Mac-Adam/weather_station_2/3dModels/hub/cover.3mf

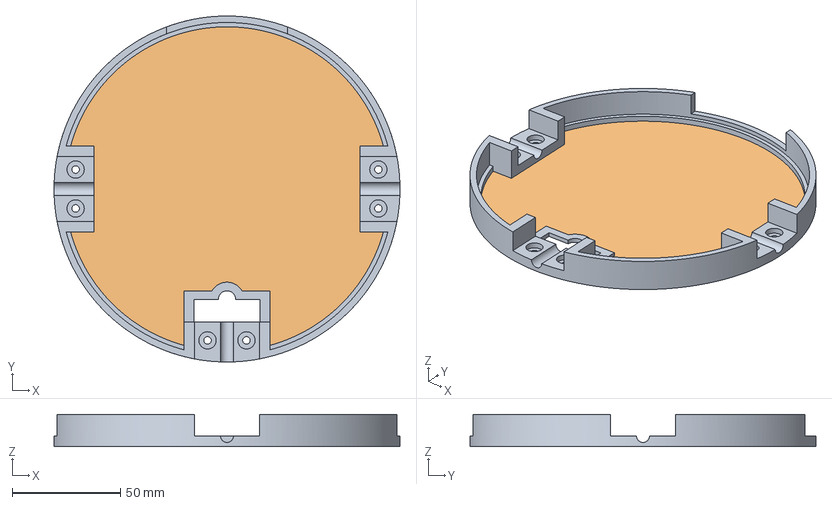
[picture p15: CAD file, 2026-03-01]
3dModels/hub/cover.3mf
160.0 x 160.0 x 15.0 mm
