Mac-Adam/weather_station_2/3dModels/rain/pools.3mf

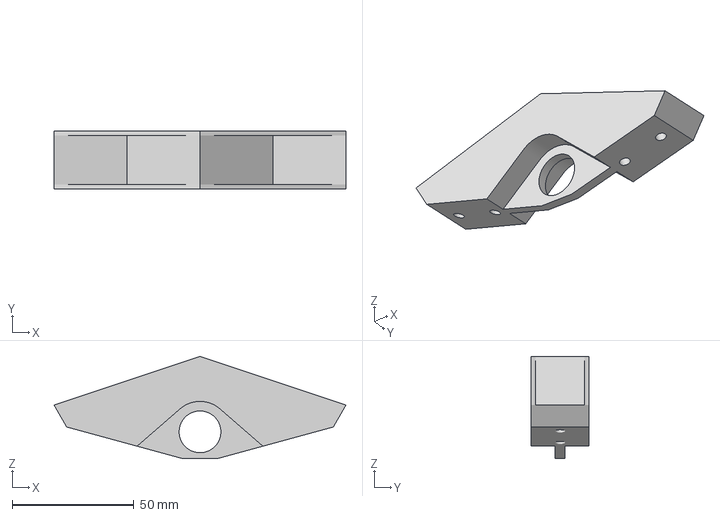
[picture p16: CAD file, 2026-03-01]
3dModels/rain/pools.3mf
120.0 x 24.0 x 42.0 mm
