Mac-Adam/weather_station_2/3dModels/wind/cover.3mf

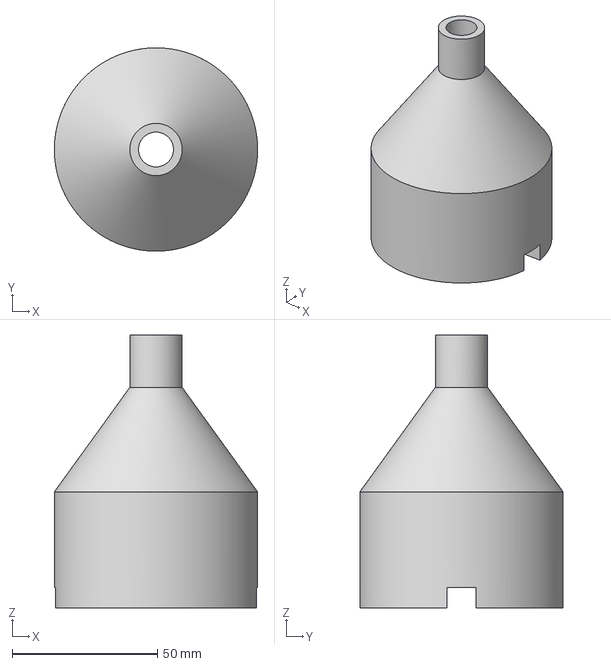
[picture p17: CAD file, 2026-03-01]
3dModels/wind/cover.3mf
70.0 x 70.0 x 94.0 mm
