Mac-Adam/weather_station_2/3dModels/rain/mout.3mf

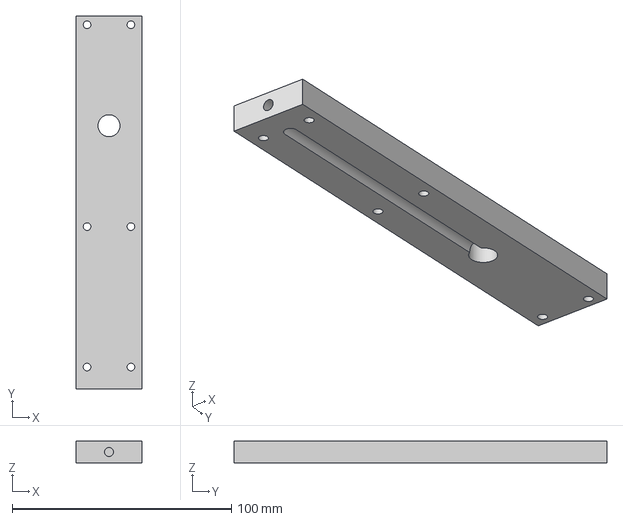
[picture p18: CAD file, 2026-03-01]
3dModels/rain/mout.3mf
30.0 x 170.0 x 10.0 mm
