Mac-Adam/weather_station_2/3dModels/wind/shaft_speed.3mf

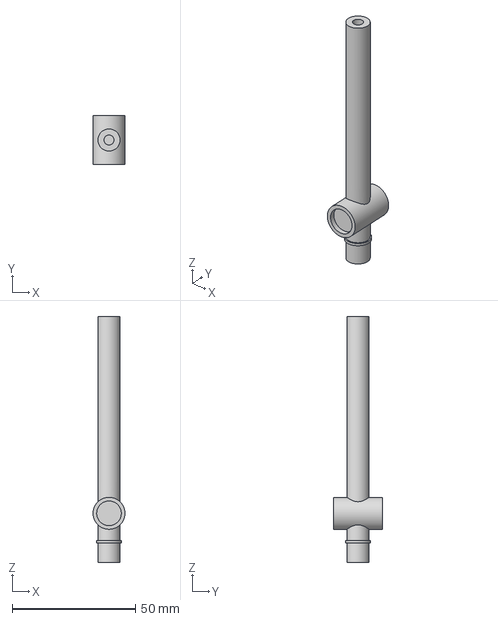
[picture p19: CAD file, 2026-03-01]
3dModels/wind/shaft_speed.3mf
13.0 x 20.0 x 100.0 mm
