Mac-Adam/weather_station_2/3dModels/hub/mount.3mf

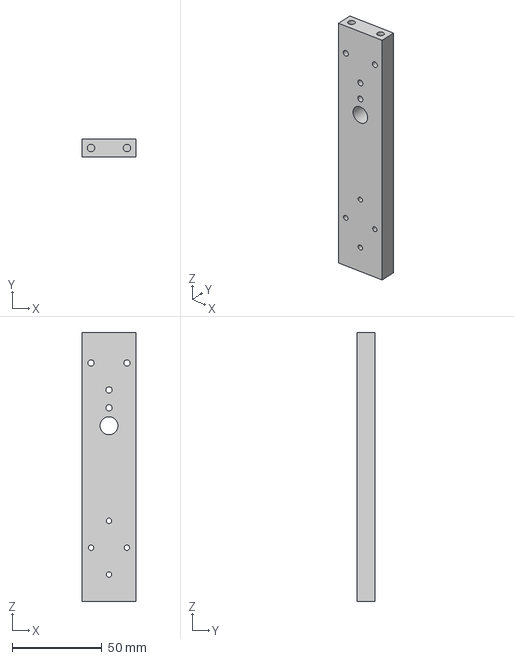
[picture p20: CAD file, 2026-03-01]
3dModels/hub/mount.3mf
30.0 x 10.0 x 150.0 mm
