Mac-Adam/weather_station_2/3dModels/rain/pin_holder.3mf

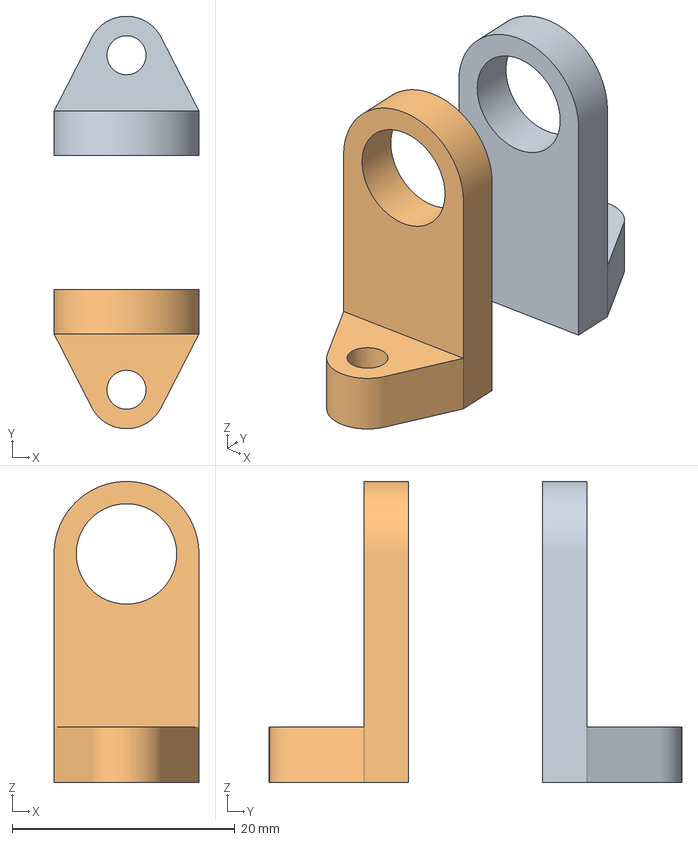
[picture p21: CAD file, 2026-03-01]
3dModels/rain/pin_holder.3mf
13.0 x 37.0 x 27.0 mm
