Mac-Adam/weather_station_2/3dModels/wind/mount.3mf

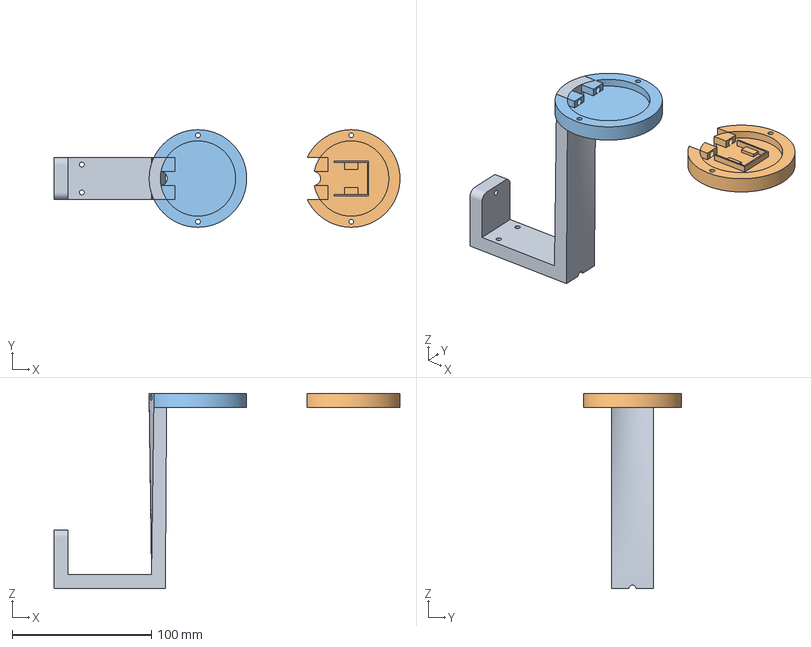
[picture p22: CAD file, 2026-03-01]
3dModels/wind/mount.3mf
248.3 x 70.0 x 140.0 mm
wind_base_mount
wind_direction_mount
wind_speed_mount
