Mac-Adam/weather_station_2/3dModels/hub/cover_minimal.3mf

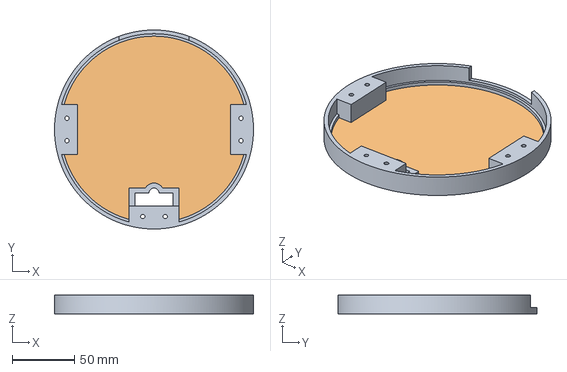
[picture p23: CAD file, 2026-03-01]
3dModels/hub/cover_minimal.3mf
160.0 x 160.0 x 15.0 mm
