Mac-Adam/weather_station_2/3dModels/rain/body.3mf

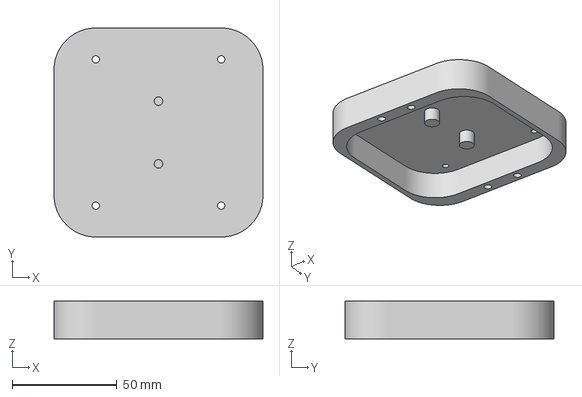
[picture p24: CAD file, 2026-03-01]
3dModels/rain/body.3mf
100.0 x 100.0 x 18.0 mm
