Mac-Adam/weather_station_2/3dModels/wind/top_cover.3mf

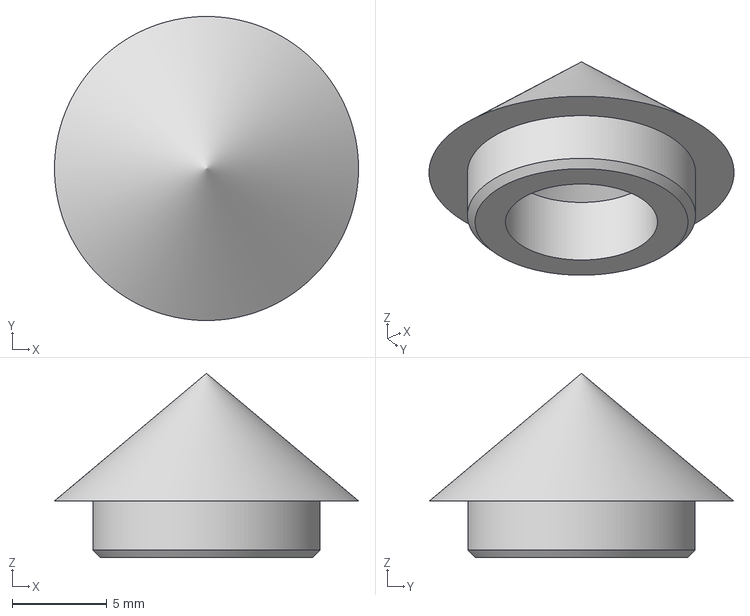
[picture p25: CAD file, 2026-03-01]
3dModels/wind/top_cover.3mf
16.1 x 16.1 x 9.73 mm
