Mac-Adam/weather_station_2/3dModels/rain/maget_holder.3mf

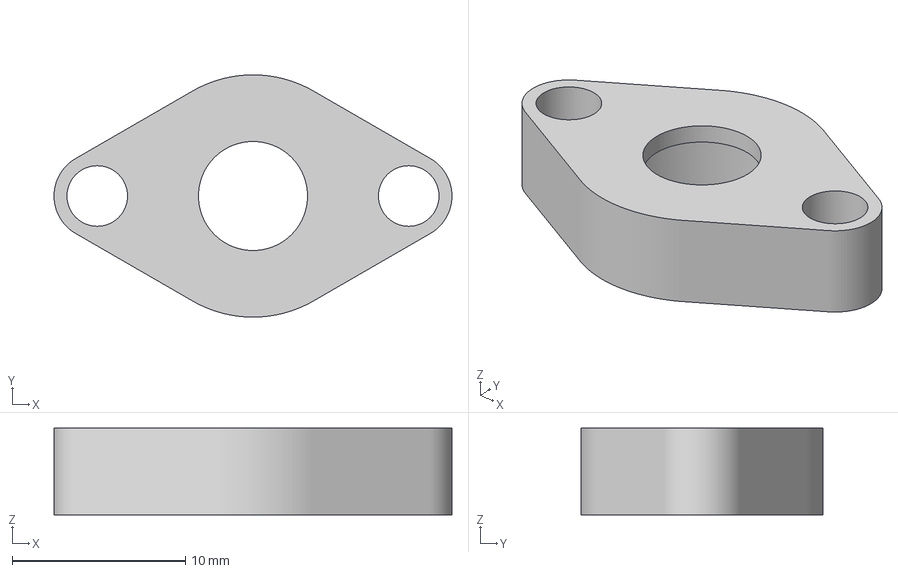
[picture p26: CAD file, 2026-03-01]
3dModels/rain/maget_holder.3mf
23.0 x 14.0 x 5.00 mm
