Mac-Adam/weather_station_2/3dModels/wind/top_direction.3mf

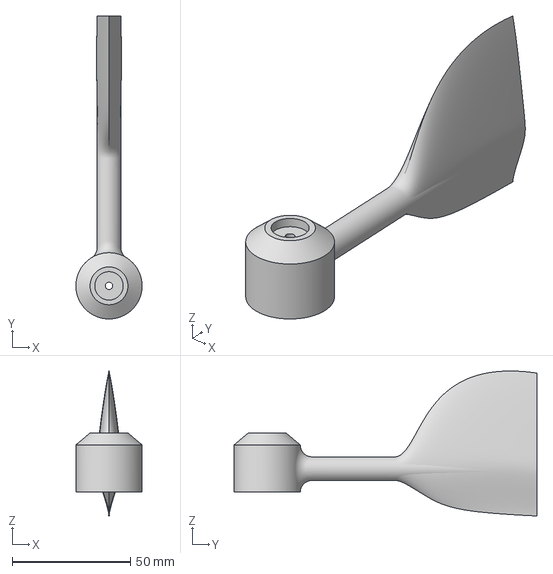
[picture p27: CAD file, 2026-03-01]
3dModels/wind/top_direction.3mf
28.0 x 128.0 x 61.3 mm
