Mac-Adam/weather_station_2/3dModels/wind/top_speed.3mf

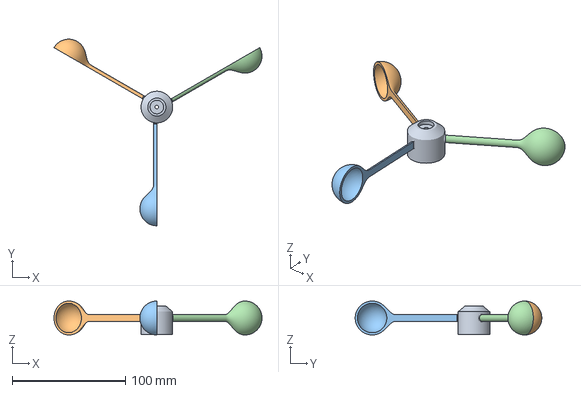
[picture p28: CAD file, 2026-03-01]
3dModels/wind/top_speed.3mf
183.9 x 165.0 x 30.0 mm
